specadmin/OM-128/PCB/Gerber_Layer_SolderMask_Bottom.png

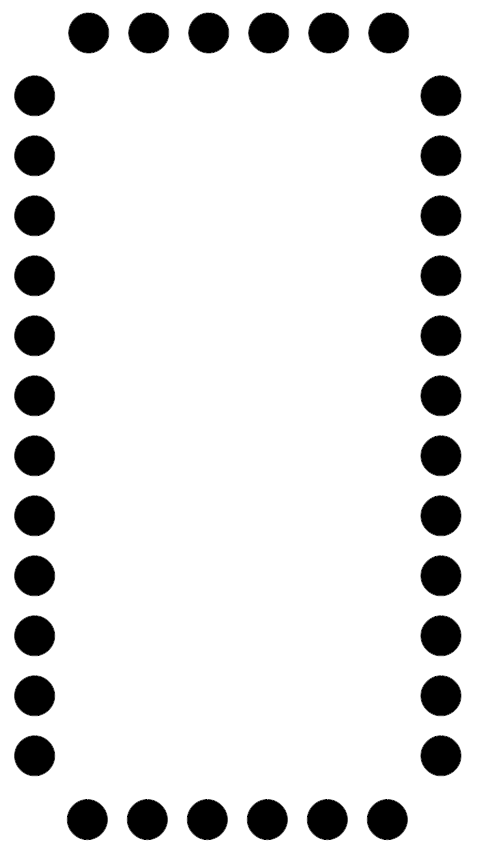
PCB/Gerber_Layer_SolderMask_Bottom.png
