specadmin/OM-128/PCB/Gerber_Layer_SolderMask_Top.png

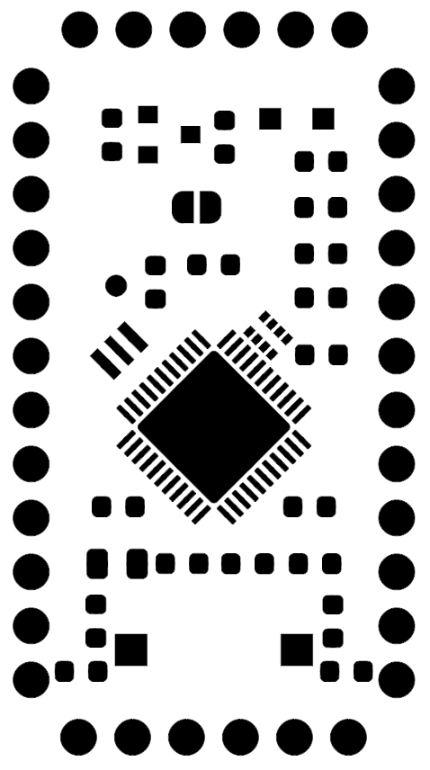
PCB/Gerber_Layer_SolderMask_Top.png
