specadmin/OM-128/firmware/include/config.h

#ifndef CONFIG_H
#define CONFIG_H
//----------------------------------------------------------------------------
#include <avr/io.h>
//----------------------------------------------------------------------------

#define DEBUG_PORT          PORTC
#define DEBUG_DDR           DDRD
#define DEBUG_BIT           7
#define DEBUG_BAUD_RATE     1152000
// #define DEBUG_EXTENDED_DUMP

//----------------------------------------------------------------------------
#endif
